TTNApeldoorn/Aid-Hittestress-2021/hardware/20210311_173719.jpg

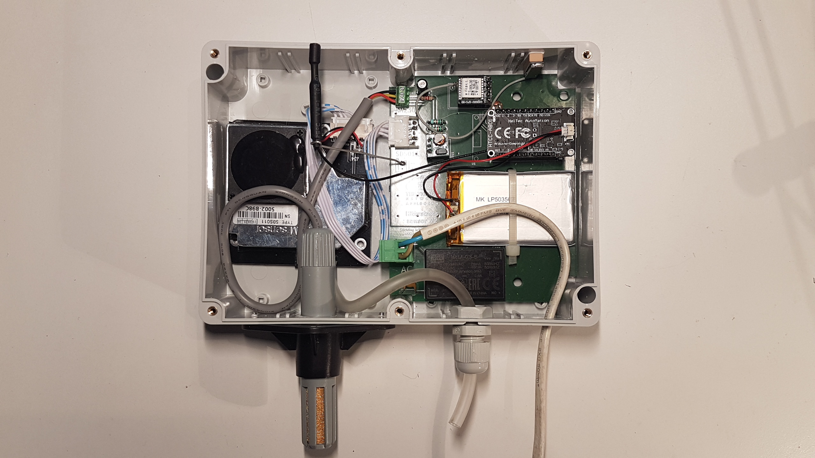
hardware/20210311_173719.jpg
